MelexinVN/bs_kombo/hardware/pcb/kombo_nrf24_atmega8/kombo_nrf24_atmega8 (2).png

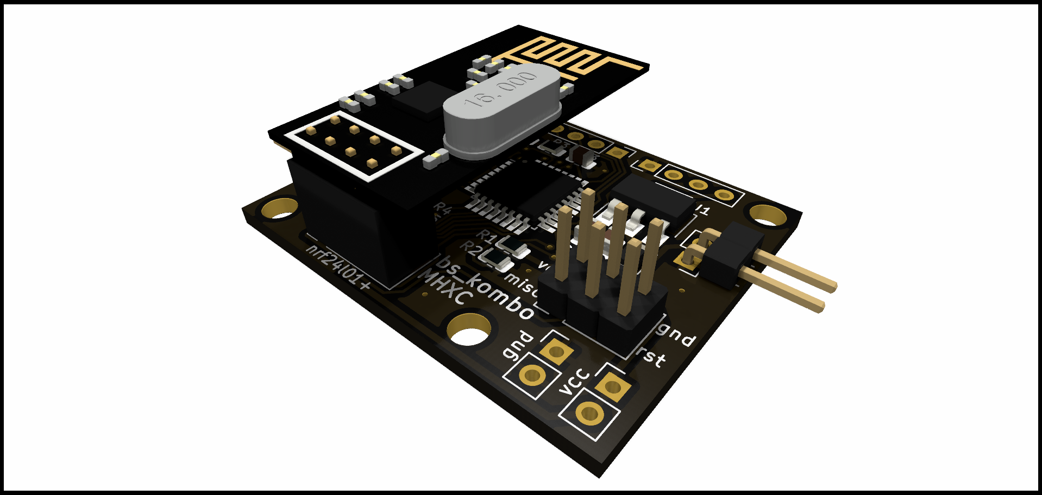
hardware/pcb/kombo_nrf24_atmega8/kombo_nrf24_atmega8 (2).png
