MelexinVN/bs_kombo/media/20221225_202203.jpg

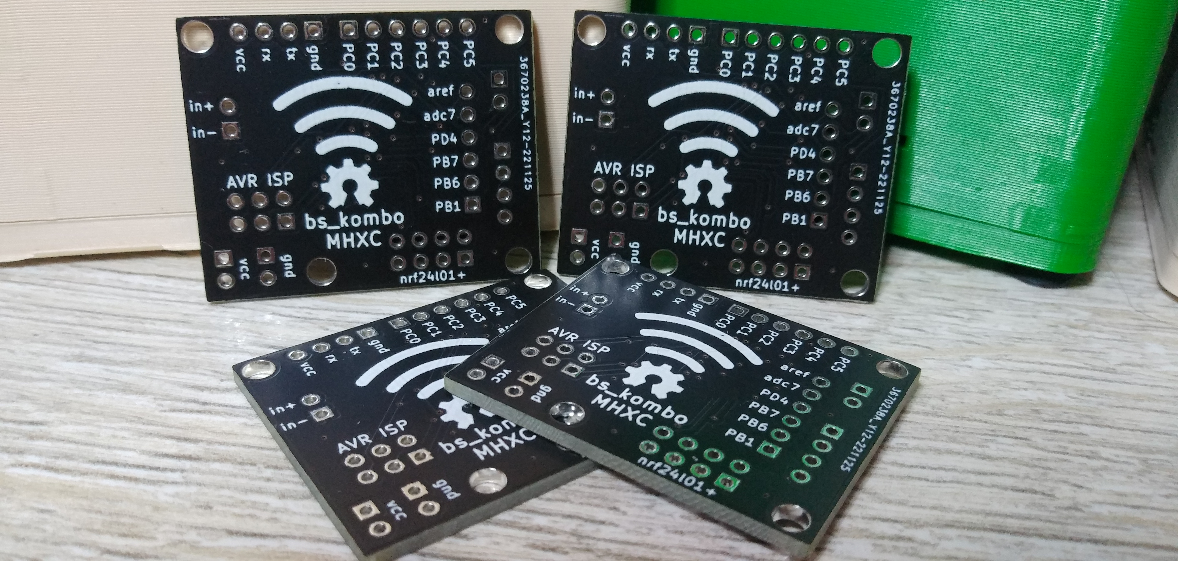
media/20221225_202203.jpg
