MelexinVN/bs_kombo/media/20221225_202310.jpg

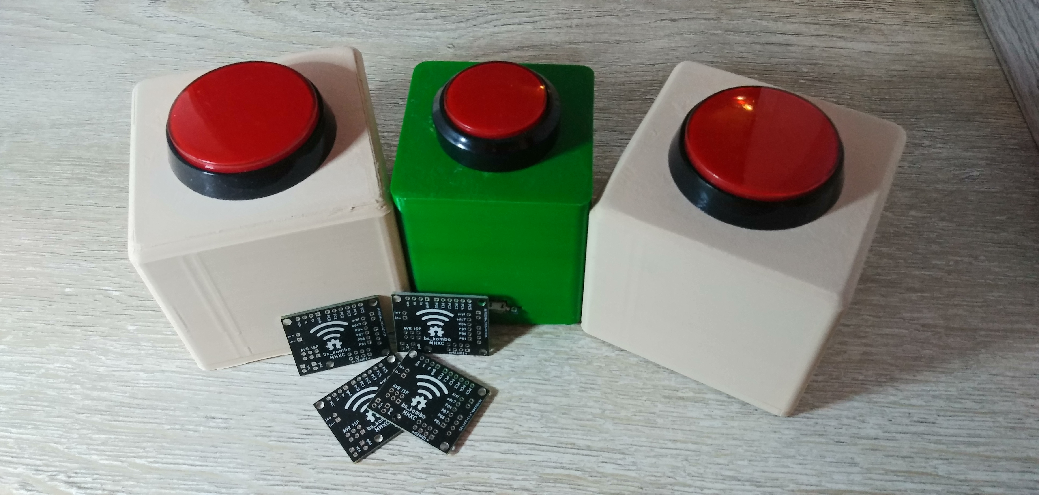
media/20221225_202310.jpg
