MelexinVN/bs_kombo/media/20221226_195855.jpg

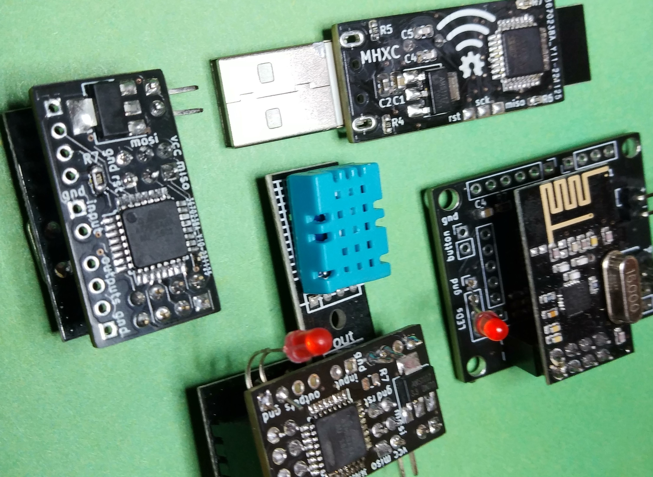
media/20221226_195855.jpg
