MelexinVN/bs_kombo/media/20221226_195855_.jpg

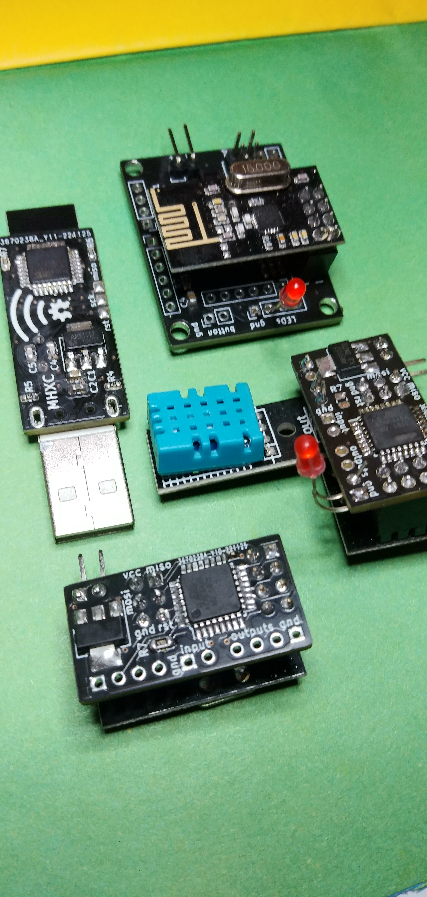
media/20221226_195855_.jpg
