MelexinVN/bs_kombo/media/20221226_200403.jpg

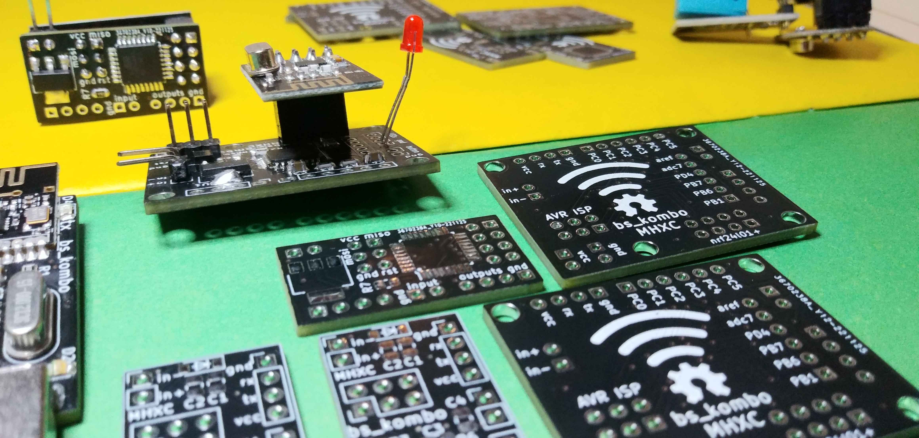
media/20221226_200403.jpg
