MelexinVN/bs_kombo/media/20221226_200708_HDR.jpg

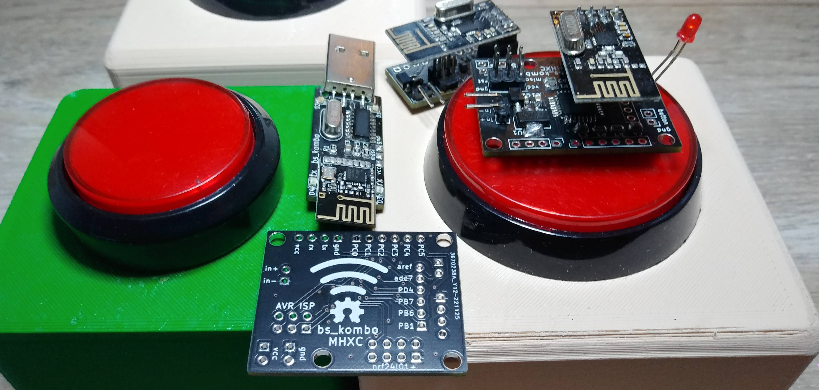
media/20221226_200708_HDR.jpg
