MelexinVN/bs_kombo/media/20221226_200926.jpg

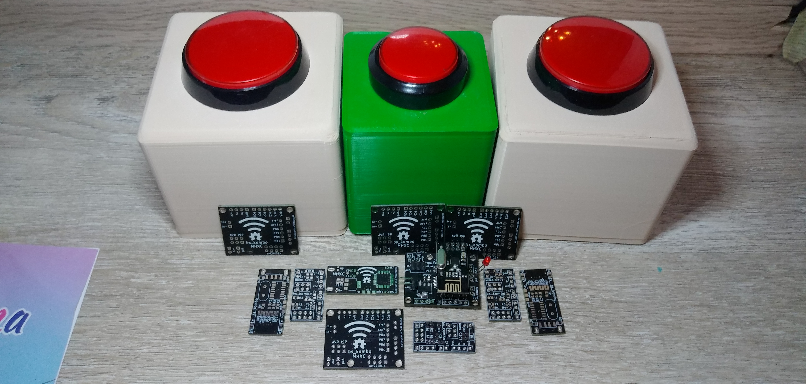
media/20221226_200926.jpg
