MelexinVN/bs_kombo/media/20221226_200952.jpg

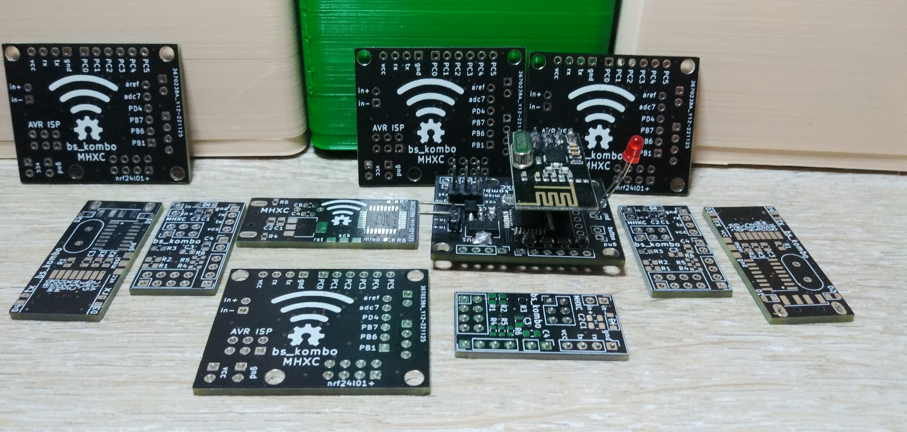
media/20221226_200952.jpg
