MelexinVN/bs_kombo/media/photo_2022-12-27_09-55-24.jpg

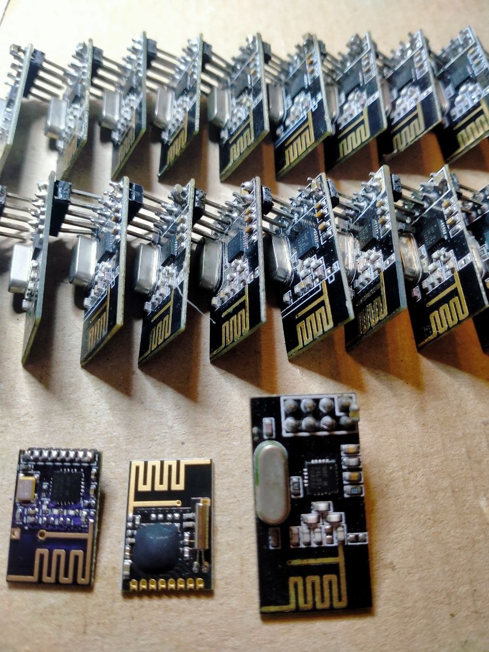
media/photo_2022-12-27_09-55-24.jpg
