MelexinVN/bs_kombo/software/examples/esp32/kombo_nrf24_test_master/README.md

## Пример создан в версии Arduino IDE v.2.1.0

### Вариант подключения:

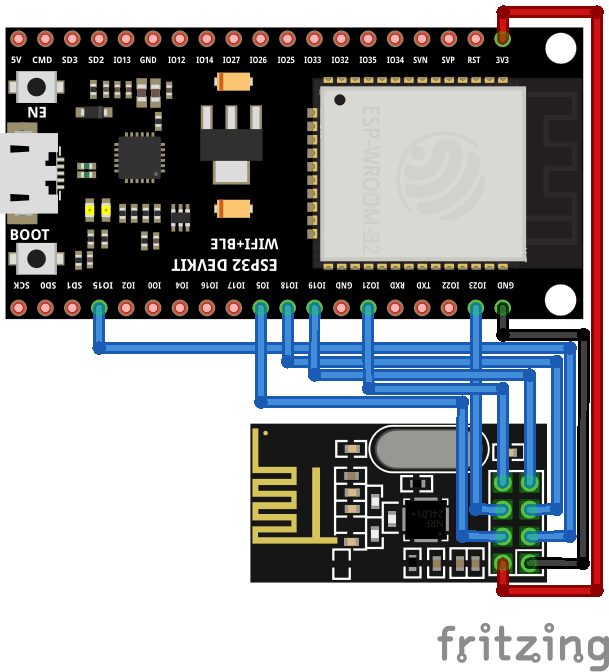
[picture p40: software/examples/esp32/kombo_nrf24_test_slave/esp32+nrf24l01_example_bb.png]
